antoinejaussoin/lastertag/projects/gun/src/board.rs

//! Shared interrupt bindings for USB, the CYW43 SPI PIO, and DMA.

use embassy_rp::bind_interrupts;
use embassy_rp::dma;
use embassy_rp::peripherals::{DMA_CH0, PIO0, USB};
use embassy_rp::pio::InterruptHandler as PioInterruptHandler;
use embassy_rp::usb::InterruptHandler as UsbInterruptHandler;

bind_interrupts!(pub struct Irqs {
    PIO0_IRQ_0 => PioInterruptHandler<PIO0>;
    USBCTRL_IRQ => UsbInterruptHandler<USB>;
    DMA_IRQ_0 => dma::InterruptHandler<DMA_CH0>;
});
